andrea-acampora/IoT-Smart-Dam/src/dam_controller/ServoMotor.cpp

#include "ServoMotor.h"
#include "Arduino.h"

ServoMotor::ServoMotor(int pin){
  this->pin = pin;  
} 

void ServoMotor::on(){
  motor.attach(pin);    
}

void ServoMotor::setPosition(int angle){
  float coeff = (2250.0-750.0)/180;
  motor.write(750 + angle*coeff);   
}

void ServoMotor::off(){
  motor.detach();    
}
