andrea-acampora/IoT-Smart-Dam/src/dam_controller/timerZero.cpp

#include "timerZero.h"

#define TIMER0_MAX_VALUE 256UL
#define CYCLES_PER_MICROSEC 16

// A function that does nothing, useful for initializing and resetting the routine called with a timer interrupt
void emptyCallback(void) {}

timerZero *timerZero::SINGLETON {};

timerZero *timerZero::getInstance(void) {
    return SINGLETON;
}

// Default constructor
timerZero::timerZero(void) {
    this->count = 0; 
    this->_clockSelectBits = 0;
    this->_isrCallback = emptyCallback;
}

void timerZero::init(void) {
    TCCR0B = _BV(WGM12); // Setting the timer mode, CTC, and disabling the timer clock source (stopping it)
    TCCR0A = 0; // No flag in this register is needed
    TIMSK0 = 0; // Disabling interrupts capture
    cli(); // Disabling interrupts, because TCNT0 setting is not an atomic operation
    TCNT0 = 0; // Resetting the timer count
    sei(); // Re-enabling interrupts
}

void timerZero::setPeriod(unsigned long int period) {
    const unsigned long int cycles = CYCLES_PER_MICROSEC * period;
    const int prescalerValues[] = { 1, 8, 64, 256, 1024 };
    const unsigned int csBitsValues[] = { _BV(CS10), _BV(CS11), _BV(CS11) | _BV(CS10), _BV(CS12), _BV(CS12) | _BV(CS10) };
    bool timerSet = false;

    for (int i = 0; i < 5 && !timerSet; i++) {
        if (cycles < TIMER0_MAX_VALUE * prescalerValues[i]) {
            /*
             * To start the timer three bits will need to be set in the TCCR1B register for the prescaler value.
             * How those bits needs to be set depends on how long the period of the timer is, because the value
             * of the period must fit the "compare match" register (OCR1A) and the prescaler is needed to downscale it.
             * Setting those bits will start the timer, so their value is temporarily stored in _clockSelectBits.
             */
            this->_clockSelectBits = csBitsValues[i]; 
            cli(); // Disabling interrupts, because OCR1A setting is not an atomic operation
            OCR0A = cycles / prescalerValues[i];//cycles / prescalerValues[i]; // Setting the value with which the counter (TCNT1) will be compared
            sei(); // Re-enabling interrupts
            timerSet = true;
        }
    }
    /*
     * If value exceeds the maximum value the register can hold, even with the maximum prescaler value, it sets the register
     * value to the maximum value.
     */
    if (!timerSet) {
        this->_clockSelectBits = _BV(CS12) | _BV(CS10);
        cli(); // Disabling interrupts, because OCR1A setting is not an atomic operation
        OCR0A = TIMER0_MAX_VALUE - 1; 
        sei(); // Re-enabling interrupts
    }
}

void timerZero::attachInterrupt(void (*isr)(void)) {
    this->_isrCallback = isr; // Setting the function to be called on the interrupt capture
    TIMSK0 |= (1 << OCIE0A);; // Enabling interrupts capture
}

void timerZero::detachInterrupt(void) {
    TIMSK0 = 0; // Disabling interrupts capture
    this->_isrCallback = emptyCallback; // Resetting function called on interrupt to an empty one
}

void timerZero::start(void) {
    TCCR0B |= this->_clockSelectBits; // Setting the clock source, and consequently starting the timer
}

void timerZero::stop(void) {
    cli(); 
    TCCR0B = _BV(WGM12);  // Disabling the timer clock source (stopping it), and setting the timer mode (CTC)
    sei(); 
}

void timerZero::reset(void) {
    cli(); // Disabling interrupts, because TCNT0 setting is not an atomic operation
    TCNT0 = 0; // Resetting the timer counter, to start a new period
    sei(); // Re-enabling interrupts
}

void (*timerZero::getCallback(void))(void) {
    return this->_isrCallback;
}

// Creating an "alias" to the singleton instance of this class so as to easily access it from the Arduino code
timerZero timer0 = *timerZero::getInstance();

/*
 * Setting that the function to be called during an interrupt generated by the timer in CTC mode is the one
 * previously set by attachInterrupt and saved into the object.
 */
ISR(TIMER0_COMPA_vect) {
     (timer0.getCallback())();
}
