andrea-acampora/IoT-Smart-Dam/src/dam_controller/Dam_Async_FSM.cpp

#include "Dam_Async_FSM.h"


Dam_Async_FSM :: Dam_Async_FSM(Light* led, Dam* dam, SerialConsole* console, ConsoleBT* consoleBT,TimerEventSource* timerEventSource){
  this -> led = led;
  this -> dam = dam;
  this -> console = console;
  this -> consoleBT = consoleBT;
  this -> timerEventSource = timerEventSource;
  this -> console -> registerObserver(this);
  this -> consoleBT -> registerObserver(this);
  this -> timerEventSource -> registerObserver(this);
  currentState = ON;
}

void Dam_Async_FSM::handleEvent(Event* ev){
  switch(currentState){
    case OFF:
        break;
    case ON:
        if(ev -> getType() == MSG_DAM_OPENING){
          this -> openDam(ev -> getMessage().toInt());
        }else if(ev -> getType() == MSG_MODE_CHANGED){
          if(ev->getMessage() == "MANUAL"){
            this -> led -> switchOn();
            timer0.stop();
          }else if(ev -> getMessage() == "AUTOMATIC"){
            this -> led -> switchOff();
            timer0.start();
          }
        }else if(ev -> getType() == TIMER_EVENT){
          this -> led -> isOn() ? this -> led -> switchOff() : this -> led -> switchOn();
        }else if(ev -> getType() == COMUNICATION_INFO){
          if(ev->getMessage() == "START"){
            this -> receivingData = true;
            timer0.start();
          }else if(ev -> getMessage() == "STOP"){
            this -> receivingData = false;
            this -> led -> switchOff();
            this->startSleepMode();
            timer0.stop();
          }
        }
        break;
  }
}

void Dam_Async_FSM::openDam(int newDamLevel){
      this -> dam -> openDam(newDamLevel);
}
