andrea-acampora/IoT-Smart-Dam/src/dam_controller/globals.h

#ifndef GLOBALS
#define GLOBALS

/**
 * Contains all the global informations.
 */

#define PIN_LED_DAM 4
#define PIN_SERVO 11

#define SERIAL_RX_PIN 0

#define BT_RX_PIN 8
#define BT_TX_PIN 9



#endif
