andrea-acampora/IoT-Smart-Dam/src/dam_controller/Event.h

#ifndef __EVENT__
#define __EVENT__

#include "Arduino.h"

#define MSG_DAM_OPENING 1
#define MSG_MODE_CHANGED 2

#define TIMER_EVENT 3
#define COMUNICATION_INFO 4
/**
 * Class representing an event
 */

class Event {

  public:
    virtual int getType() = 0;
    virtual String getMessage() = 0;
};

#endif
