andrea-acampora/IoT-Smart-Dam/src/dam_controller/Led.cpp

#include "Led.h"

Led::Led(int pin){
    this->pin = pin; 
    pinMode(pin, OUTPUT); 
}

void Led::switchOn(){
    digitalWrite(pin, HIGH); 
}

void Led::switchOff(){
    digitalWrite(pin, LOW); 
}; 

bool Led::isOn(){
    return digitalRead(pin)==HIGH;
}; 
