andrea-acampora/IoT-Smart-Dam/src/dam_controller/Led.h

#ifndef __LED__
#define __LED__

#include "Light.h"
#include "Arduino.h"

class Led: public Light{
    public: 
        Led(int pin); 
        void switchOn(); 
        void switchOff();
        bool isOn();
    private: 
        int pin; 
}; 

#endif
