andrea-acampora/IoT-Smart-Dam/src/dam_remotehydrometer/WaterLevel.cpp

#include "WaterLevel.h"


WaterLevel::WaterLevel(){
  this-> stateChanged = false;
}

float WaterLevel::getWaterLevel(){
    return this->level; 
}

void WaterLevel::setWaterLevel(float level){
    this->level = level; 
    this->setState(); 
}

bool WaterLevel::isNormal(){
  return this->state==NORMAL;
}

bool WaterLevel::isPreAlarm(){
  return this->state==PRE_ALARM;
}

bool WaterLevel::isAlarm(){
  return this->state==ALARM;
}

void WaterLevel::setState(){
    String oldState = this -> getState();
    Serial.print("oldState: ");
    Serial.println(oldState);
    if(this->level > PRE_ALARM_LEVEL){
        if(this->level > ALARM_LEVEL){
            this->state = ALARM; 
        }else{
            this->state = PRE_ALARM; 
        }
    }else{
        this->state = NORMAL;
    }
   Serial.print("currentState: ");
  Serial.println(this->getState());
    if(this -> getState() != oldState){
      this -> stateChanged = true;
    }else{
      this -> stateChanged = false;
    }
}

String WaterLevel::getState(){
  if(this->isNormal()){
    return "NORMAL";
  }else if(this->isPreAlarm()){
    return "PRE_ALARM";
  }else if(this->isAlarm()){
    return "ALARM";
  }
}

bool WaterLevel::isStateChanged(){
  return this -> stateChanged;
}
