andrea-acampora/IoT-Smart-Dam/src/dam_remotehydrometer/WaterLevel.h

#ifndef WATER_LEVEL
#define WATER_LEVEL


#define PRE_ALARM_LEVEL 400 
#define ALARM_LEVEL 460
#include "Arduino.h"

class WaterLevel
{
private:
    enum {NORMAL, PRE_ALARM, ALARM} state; 
    float level;
    void setState();
    bool stateChanged;
public:
    WaterLevel();
    float getWaterLevel(); 
    bool isNormal();
    bool isPreAlarm();
    bool isAlarm();
    void setWaterLevel(float level); 
    String getState();
    bool isStateChanged();
};
#endif
