andrea-acampora/IoT-Smart-Dam/src/dam_remotehydrometer/globals.h

#ifndef GLOBALS
#define GLOBALS

#define FREQ_1 10000
#define FREQ_2 5000

/**
 * Contains all the global Experiment informations.
 */
#define SONAR_TRIGGER_PIN D6
#define SONAR_ECHO_PIN D7
#define PIN_LED_ALARM D2
#define PIN_TEMP A0

#define GROUND_DISTANCE 500

#endif
