andrea-acampora/IoT-Smart-Dam/src/dam_controller/Observer.h

#ifndef __OBSERVER__
#define __OBSERVER__

#include "Event.h"

/**
 * Class representing event observers, observing Event.
 */
class Observer {
    
  public:
    virtual void notifyEvent(Event* ev);    
};

#endif;
